hidsh/ParastiPC/img/usb-bay-holder.jpg

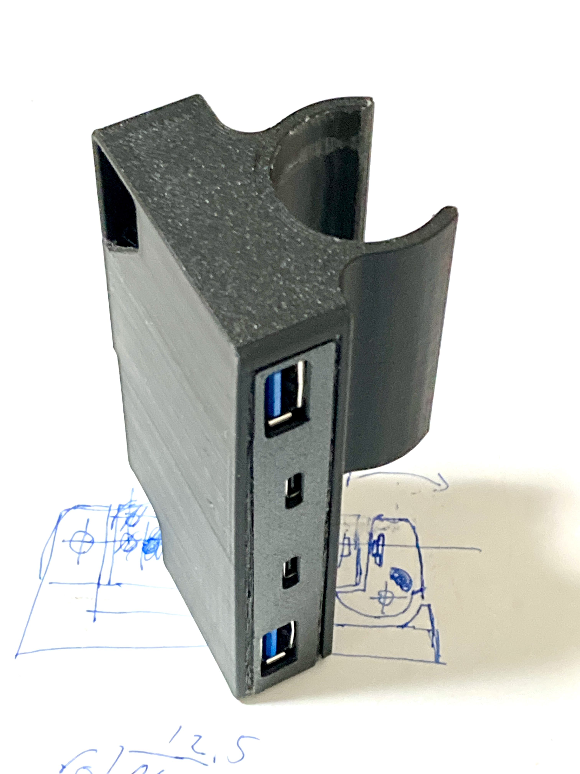
img/usb-bay-holder.jpg
